worksasdesigned/PUCK_RACER/data/img_ball.webp

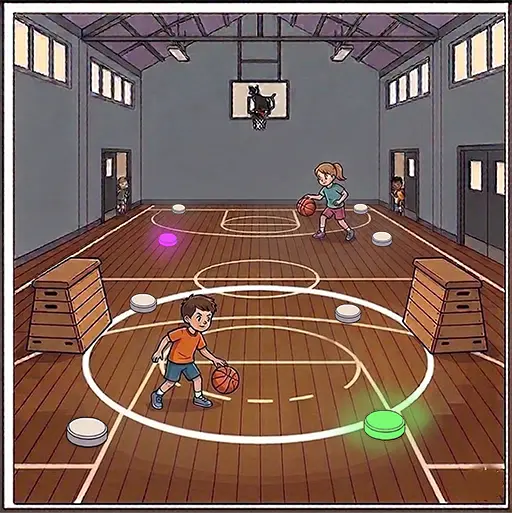
data/img_ball.webp
