worksasdesigned/PUCK_RACER/data/img_beep.webp

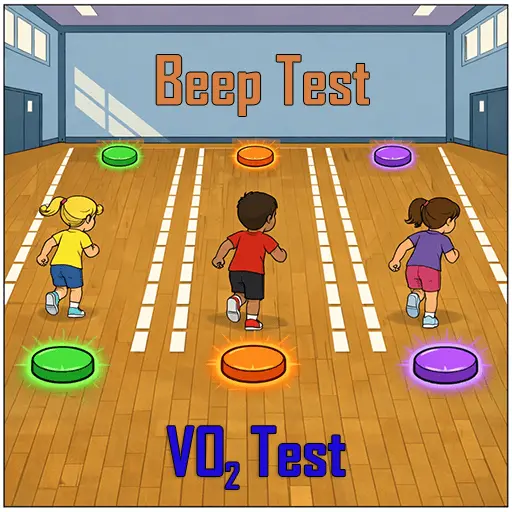
data/img_beep.webp
