worksasdesigned/PUCK_RACER/data/img_bomb.webp

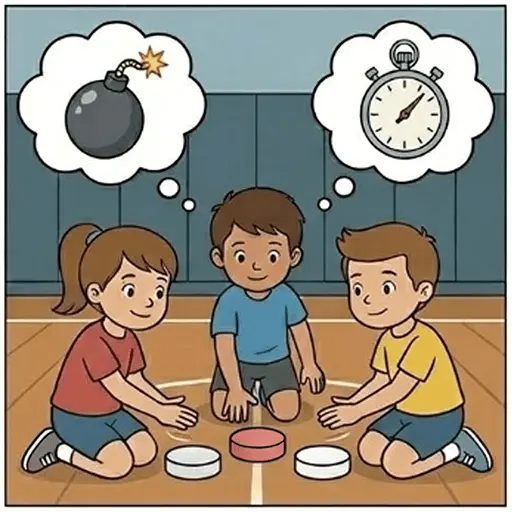
data/img_bomb.webp
