worksasdesigned/PUCK_RACER/data/img_countdown.webp

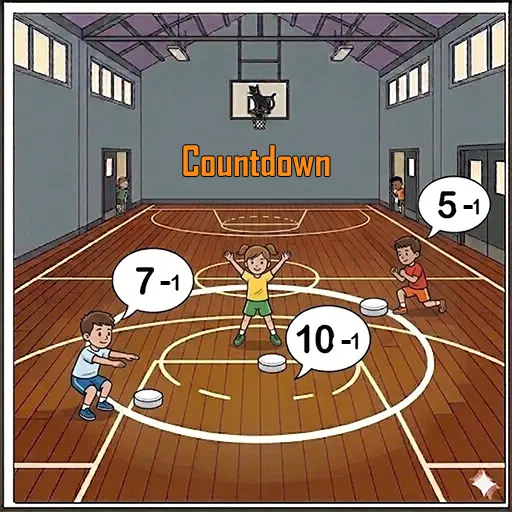
data/img_countdown.webp
