worksasdesigned/PUCK_RACER/data/img_ctl.webp

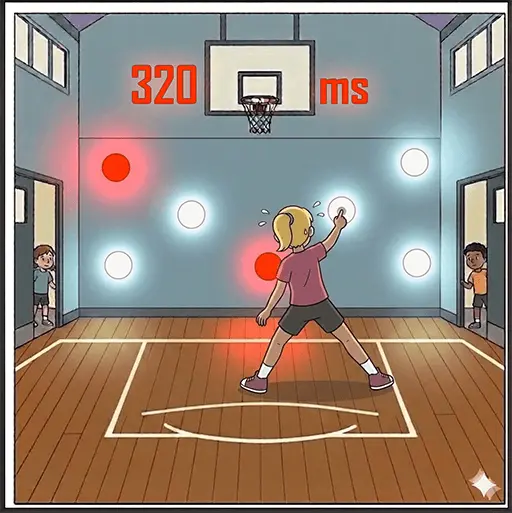
data/img_ctl.webp
