worksasdesigned/PUCK_RACER/data/img_display.webp

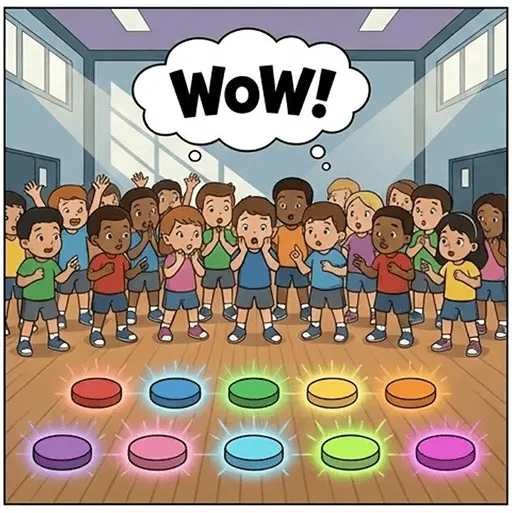
data/img_display.webp
