worksasdesigned/PUCK_RACER/data/img_domination.webp

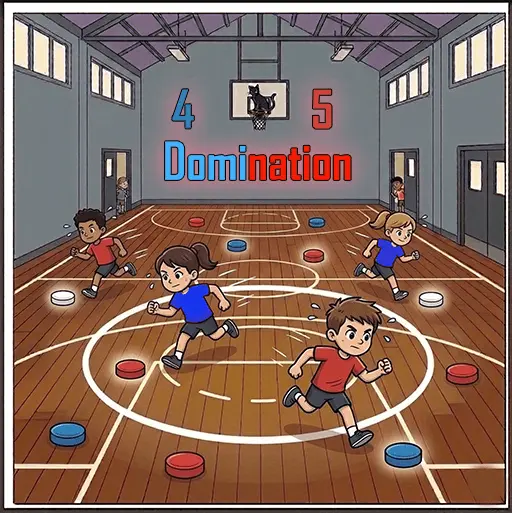
data/img_domination.webp
