worksasdesigned/PUCK_RACER/data/img_gear.webp

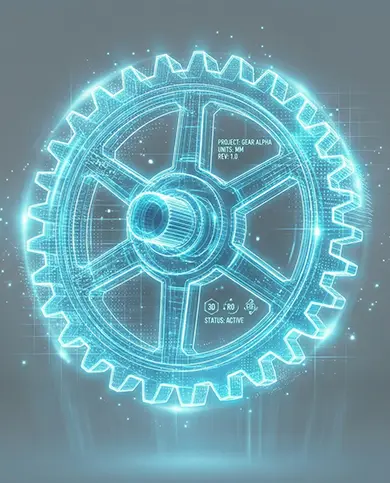
data/img_gear.webp
