worksasdesigned/PUCK_RACER/data/img_hunt.webp

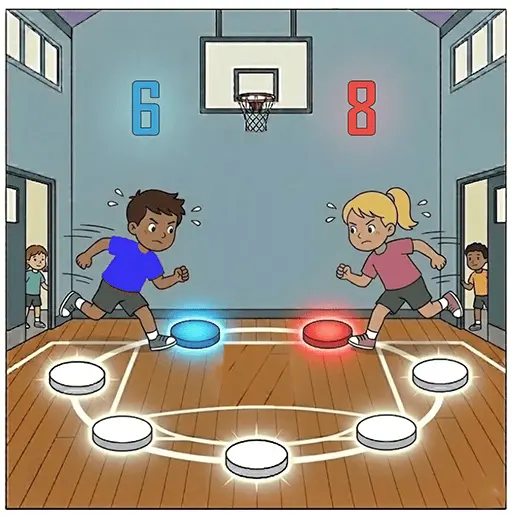
data/img_hunt.webp
