worksasdesigned/PUCK_RACER/data/img_memory.webp

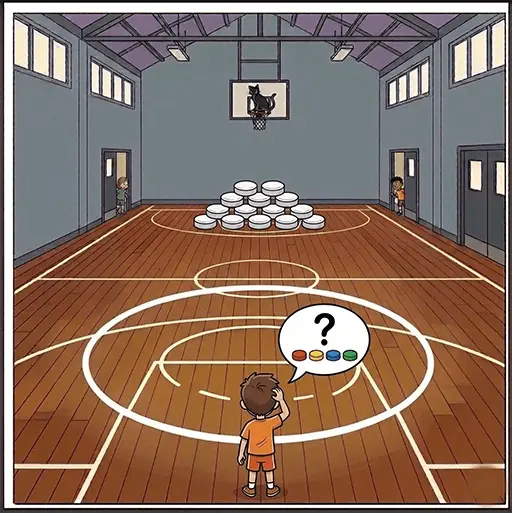
data/img_memory.webp
