worksasdesigned/PUCK_RACER/data/img_musical.webp

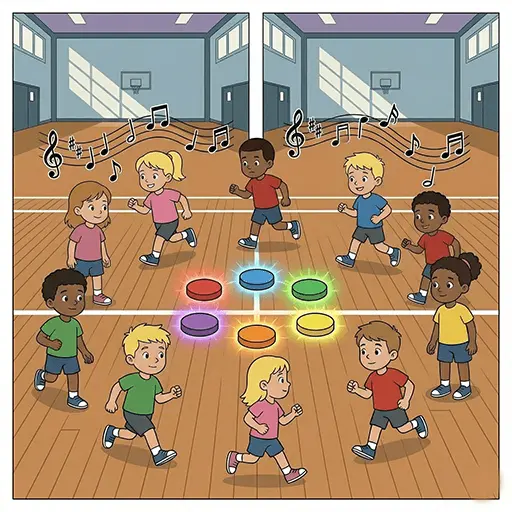
data/img_musical.webp
