worksasdesigned/PUCK_RACER/data/img_pacemaker.webp

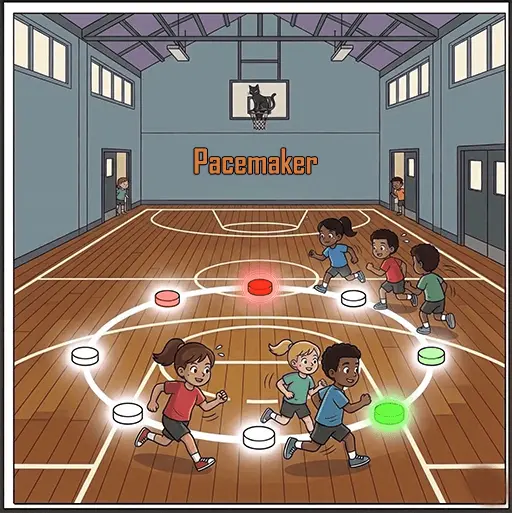
data/img_pacemaker.webp
