worksasdesigned/PUCK_RACER/data/img_pitstop.webp

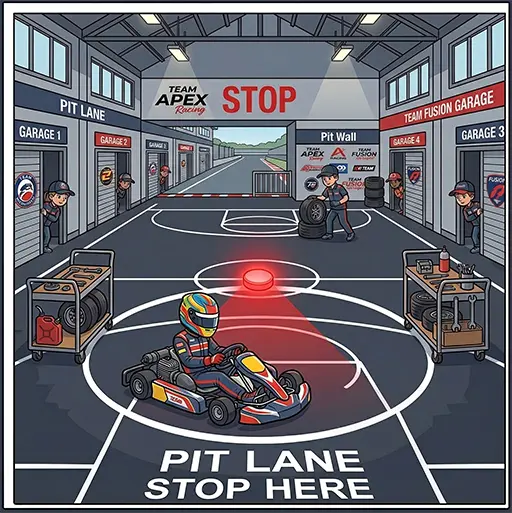
data/img_pitstop.webp
