worksasdesigned/PUCK_RACER/data/img_players.webp

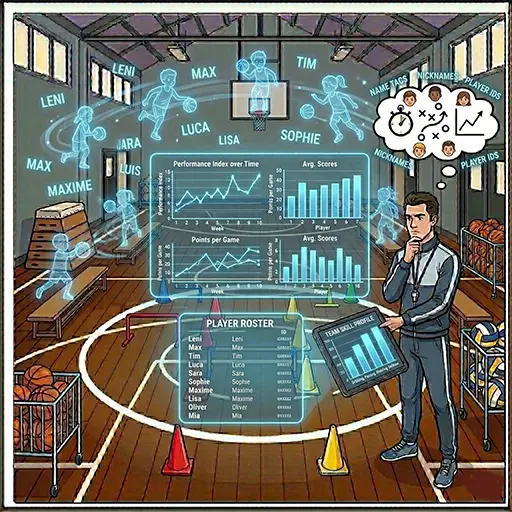
data/img_players.webp
