worksasdesigned/PUCK_RACER/data/img_react2p.webp

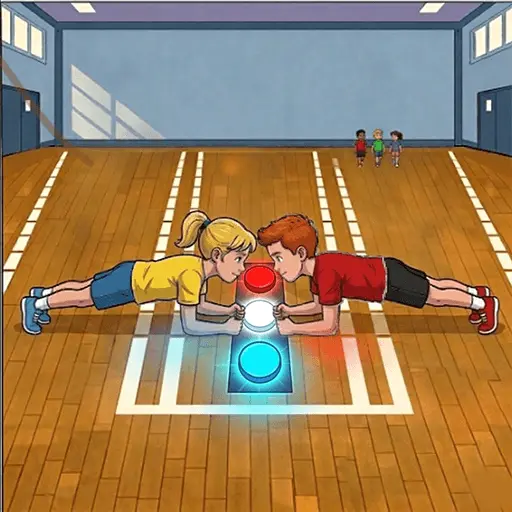
data/img_react2p.webp
