worksasdesigned/PUCK_RACER/data/img_redgreen.webp

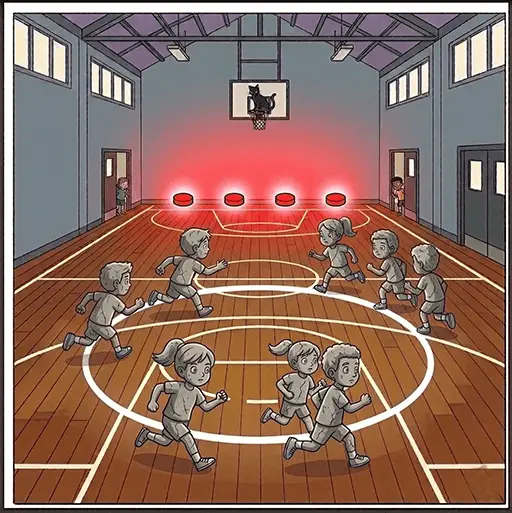
data/img_redgreen.webp
