worksasdesigned/PUCK_RACER/data/img_settings.webp

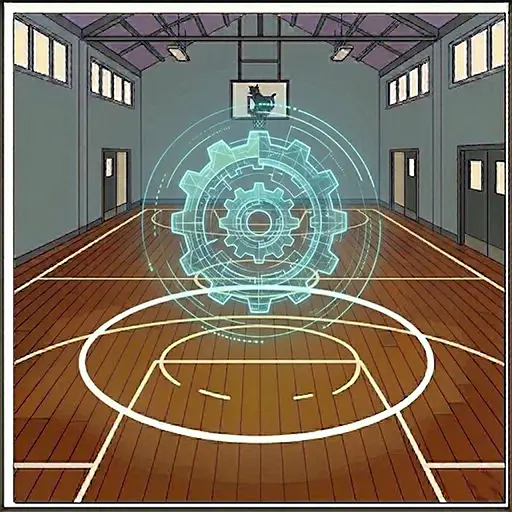
data/img_settings.webp
