worksasdesigned/PUCK_RACER/data/img_shuttle.webp

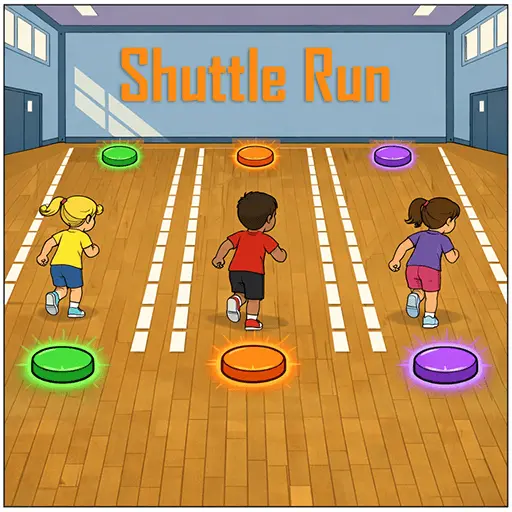
data/img_shuttle.webp
