worksasdesigned/PUCK_RACER/data/img_simon.webp

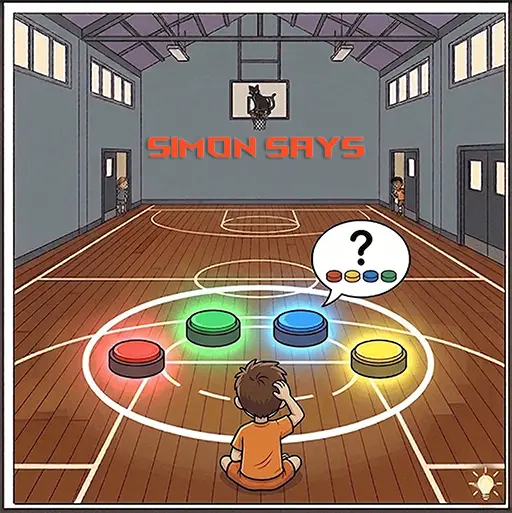
data/img_simon.webp
