worksasdesigned/PUCK_RACER/data/img_simonruns.webp

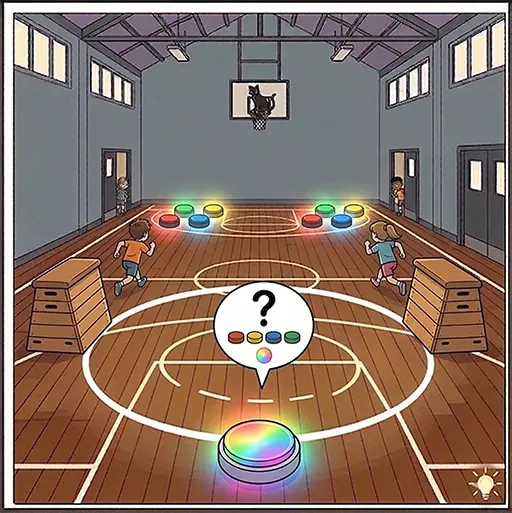
data/img_simonruns.webp
