worksasdesigned/PUCK_RACER/data/img_sorting.webp

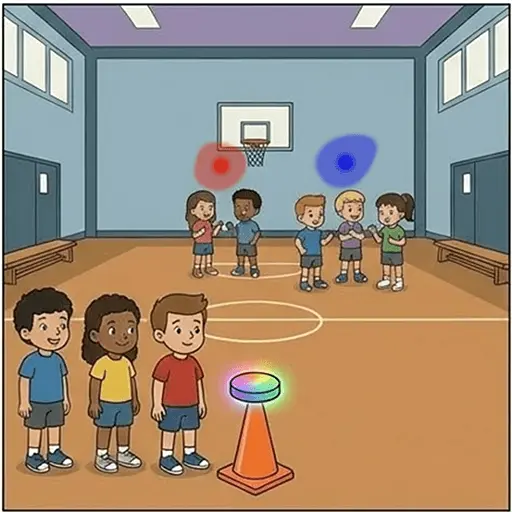
data/img_sorting.webp
