worksasdesigned/PUCK_RACER/data/img_stopwatch.webp

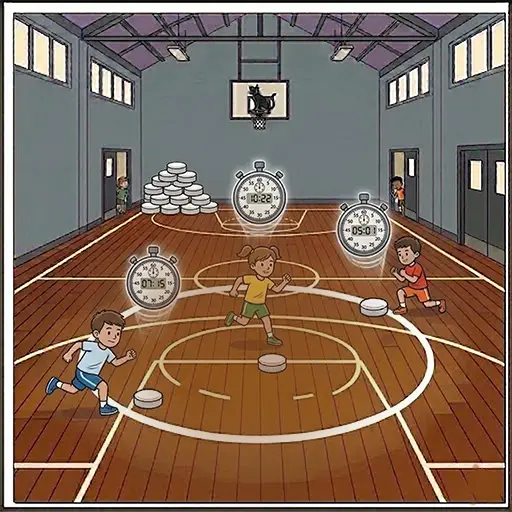
data/img_stopwatch.webp
