worksasdesigned/PUCK_RACER/data/img_tabata.webp

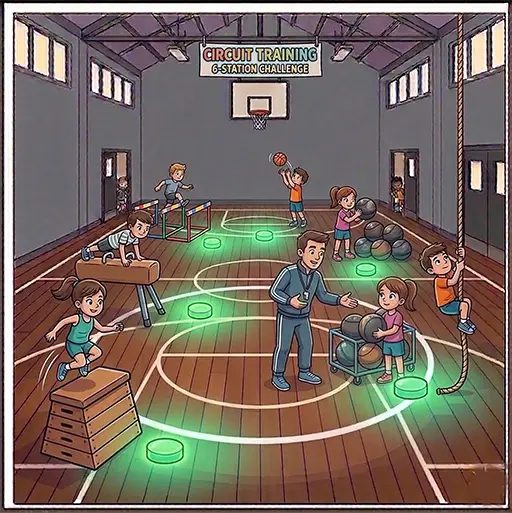
data/img_tabata.webp
