worksasdesigned/PUCK_RACER/data/img_target.webp

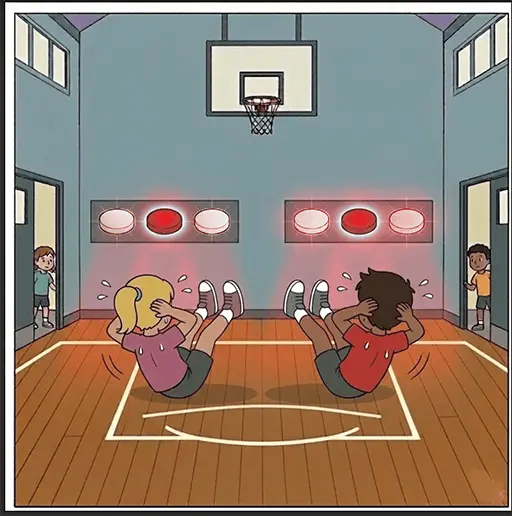
data/img_target.webp
