worksasdesigned/PUCK_RACER/data/img_timer.webp

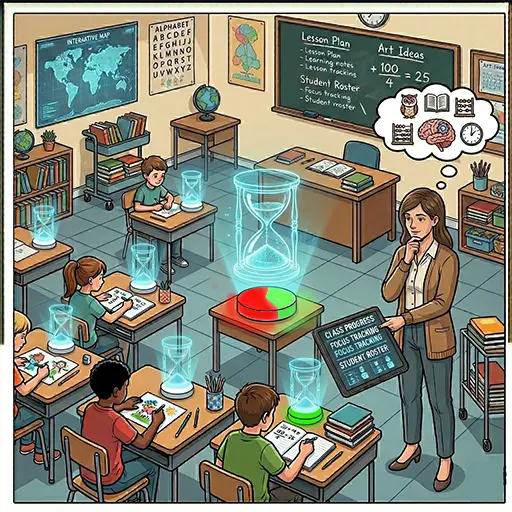
data/img_timer.webp
