worksasdesigned/PUCK_RACER/data/img_training.webp

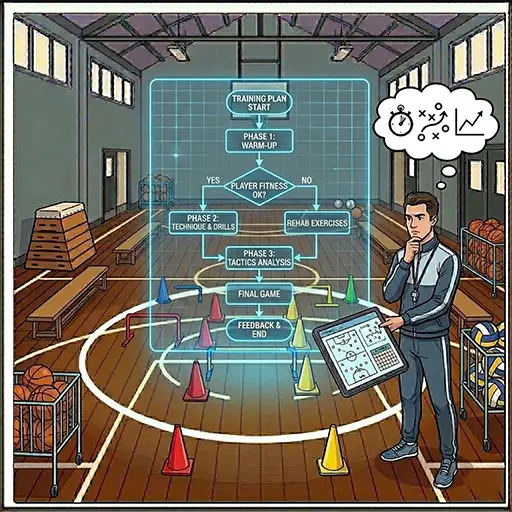
data/img_training.webp
