worksasdesigned/PUCK_RACER/data/img_tttt.webp

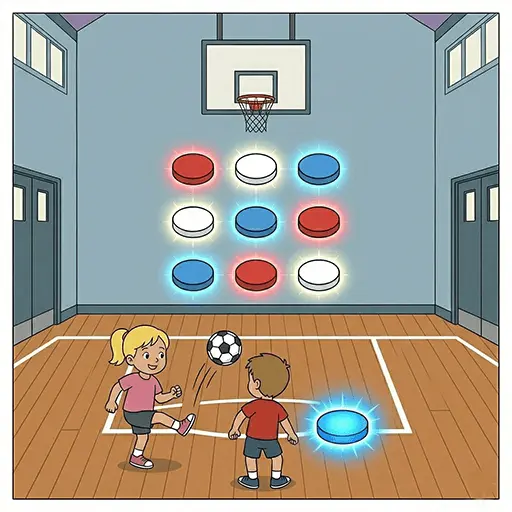
data/img_tttt.webp
