worksasdesigned/PUCK_RACER/data/img_whac.webp

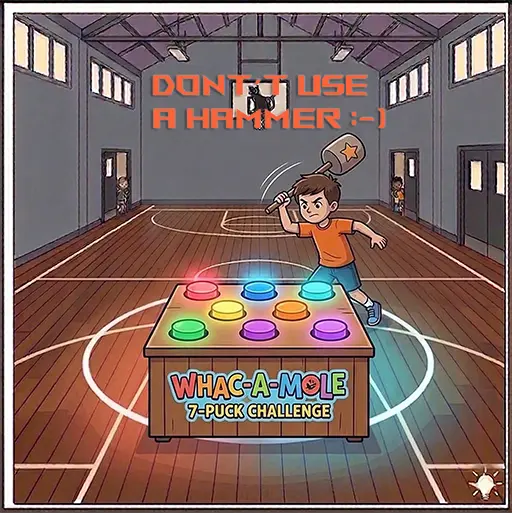
data/img_whac.webp
