worksasdesigned/PUCK_RACER/data/img_zombie.webp

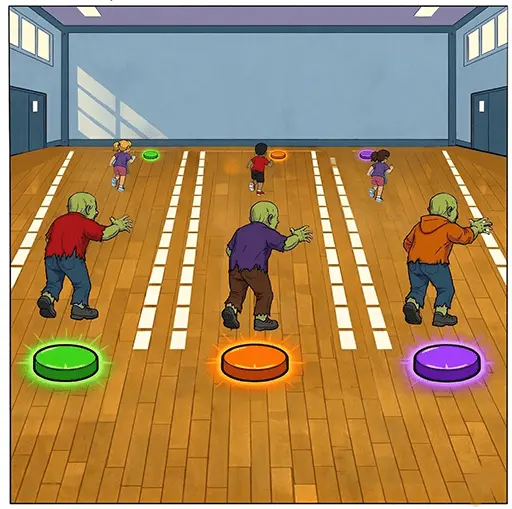
data/img_zombie.webp
