worksasdesigned/PUCK_RACER/webseite/pictures/front1_tech.png

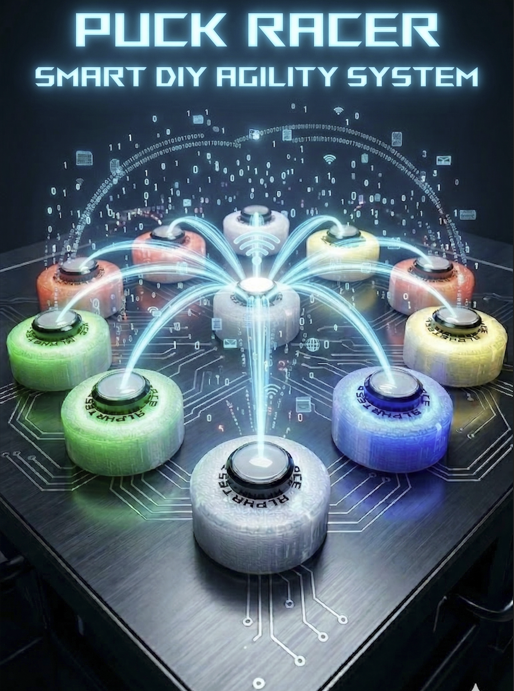
webseite/pictures/front1_tech.png
