worksasdesigned/PUCK_RACER/webseite/pictures/puck.png

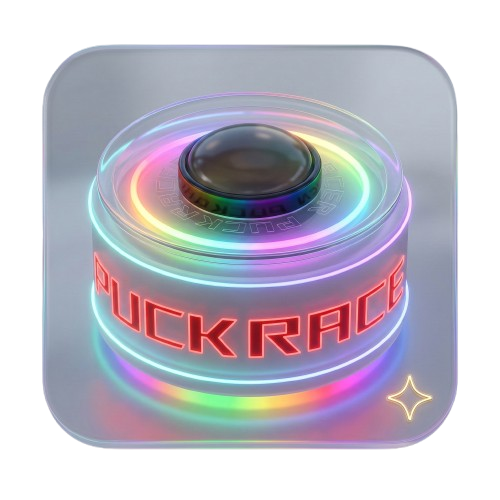
webseite/pictures/puck.png
