worksasdesigned/PUCK_RACER/webseite/pictures/server_klein.png

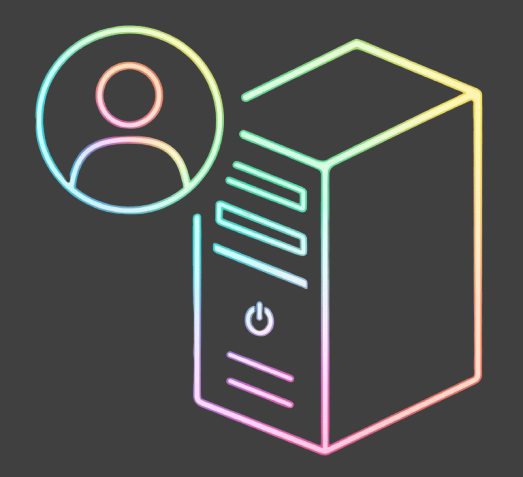
webseite/pictures/server_klein.png
