worksasdesigned/PUCK_RACER/webseite/pictures/wecker_klein.png

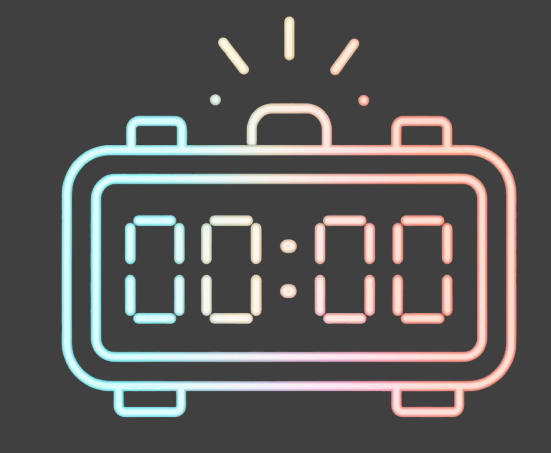
webseite/pictures/wecker_klein.png
