worksasdesigned/PUCK_RACER/webseite/pictures/weltkarte.png

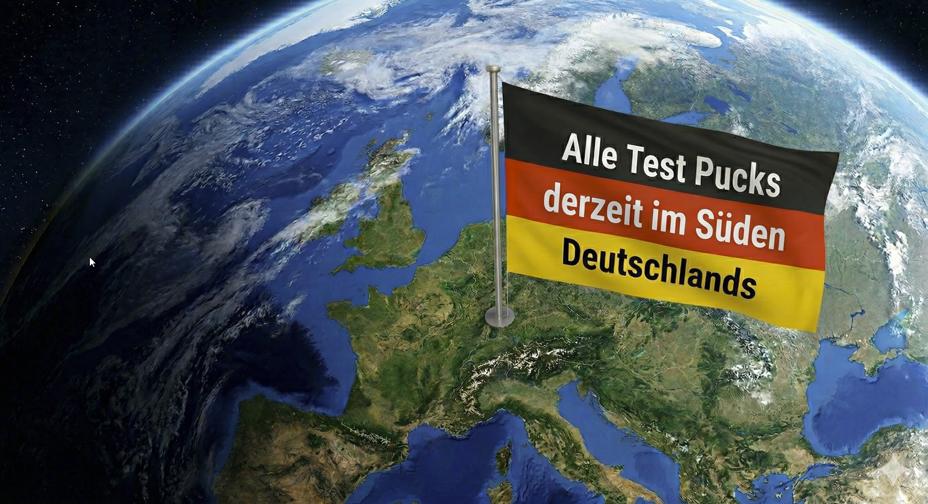
webseite/pictures/weltkarte.png
