worksasdesigned/PUCK_RACER/webseite/pictures/werkzeug_klein.png

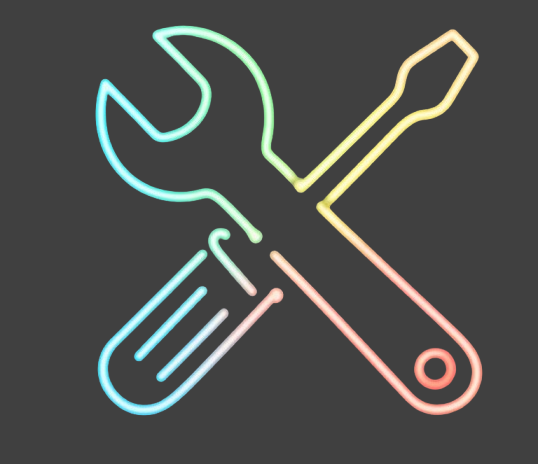
webseite/pictures/werkzeug_klein.png
