worksasdesigned/PUCK_RACER/webseite/web-app-manifest-192x192.png

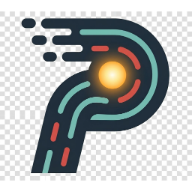
webseite/web-app-manifest-192x192.png
